JNSRYA006/EEE3088F_HAT/Simulation/Power Module/Input-Voltage-Polarity-Protection-2V_Input.jpg

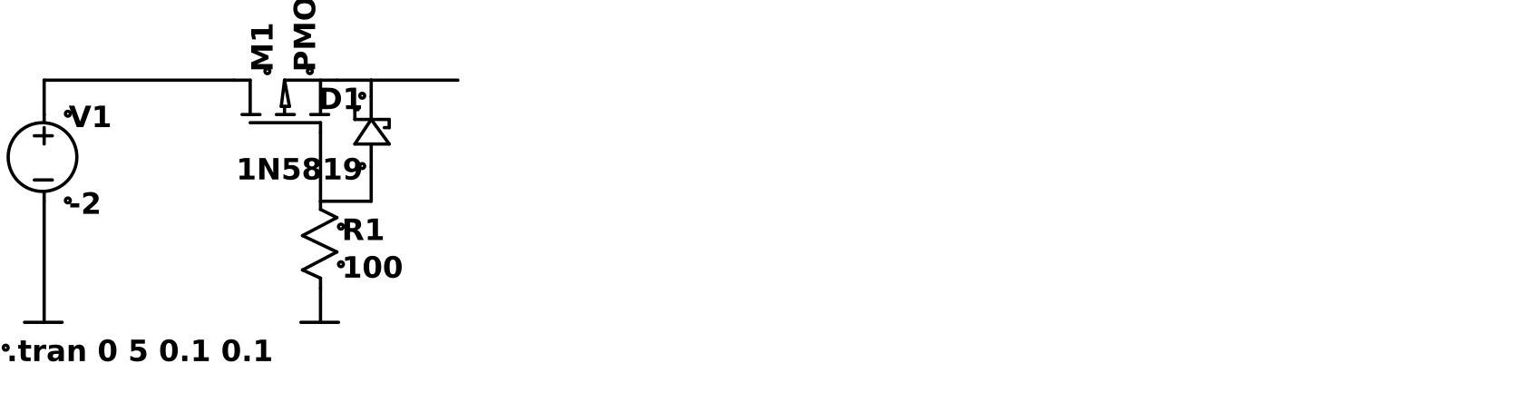
Simulation/Power Module/Input-Voltage-Polarity-Protection-2V_Input.jpg
