JNSRYA006/EEE3088F_HAT/Simulation/Power Module/Voltage Regulation/Battery Polarity Protector.asc

D1: schottky; 1N5819
M1: pmos
R1: res; 100
V1: voltage; 3.8
V2: battery; 3.65
Named nets: 0
.tran 0 5 0.1 0.1
