JNSRYA006/EEE3088F_HAT/Simulation/Power Module/Voltage Regulation/Input Voltage Polarity Protection.asc

D1: schottky; 1N5819
M1: pmos
R1: res; 100
V1: voltage; -5.5
Named nets: 0
.tran 0 5 0.1 0.1
